quocanhcgd/Voron-0/VORON-0/STLs/V0_TopHat/TopHat_Panel_Mounting/For_3mm_Panels/3mm_TH_Lower_Corner_Clip_Right_x2.stl

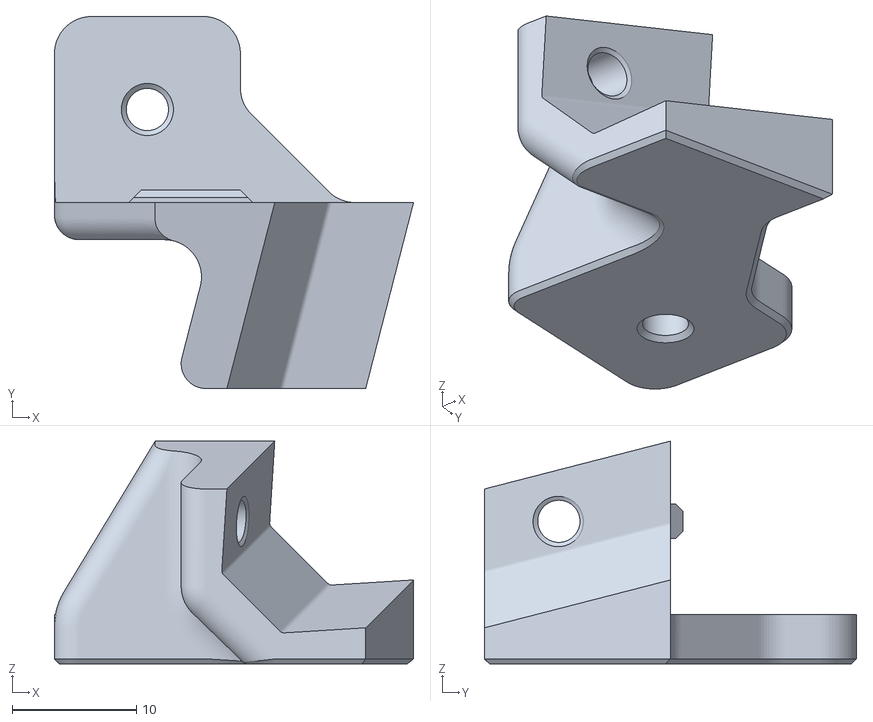
[picture p15: CAD file, 2021-10-14]
VORON-0/STLs/V0_TopHat/TopHat_Panel_Mounting/For_3mm_Panels/3mm_TH_Lower_Corner_Clip_Right_x2.stl
29.0 x 30.0 x 18.0
