quocanhcgd/Voron-0/VORON-0/STLs/V0_TopHat/Unibody_Tophat/Unibody_Tophat_x1.STL

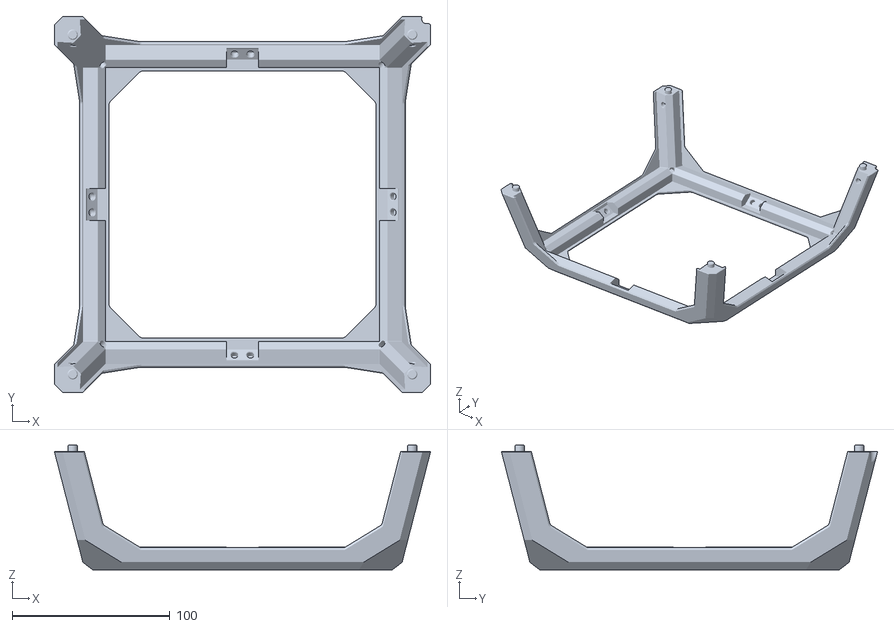
[picture p16: CAD file, 2021-10-14]
VORON-0/STLs/V0_TopHat/Unibody_Tophat/Unibody_Tophat_x1.STL
238.1 x 238.1 x 79.0
