quocanhcgd/Voron-0/VORON_Pocketwatch/STLs/[a]_Mount_Bracket_x1.STL

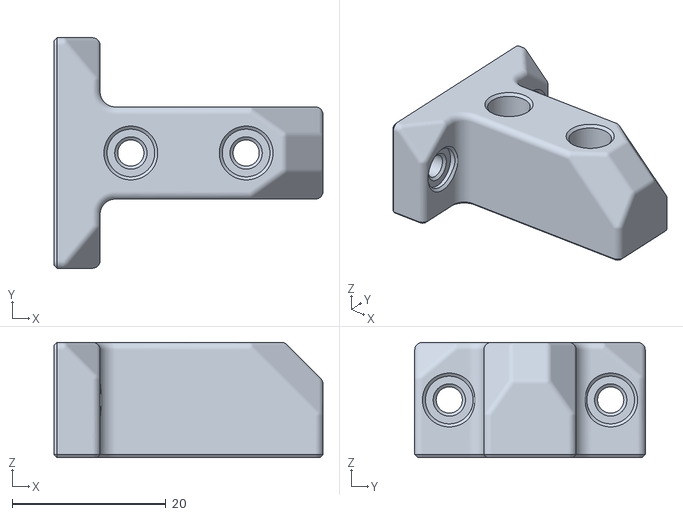
[picture p17: CAD file, 2021-10-14]
VORON_Pocketwatch/STLs/[a]_Mount_Bracket_x1.STL
35.0 x 30.0 x 15.0
