quocanhcgd/Voron-0/VORON-0/DXFs/Back_Panel_V0.DXF

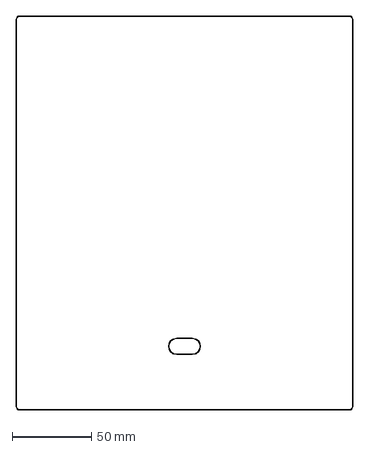
[picture p18: CAD file, 2021-10-14]
VORON-0/DXFs/Back_Panel_V0.DXF
212.0 x 248.0 mm
