quocanhcgd/Voron-0/VORON-0/STLs/[a]_A_Drive_Tensioner_x1.STL

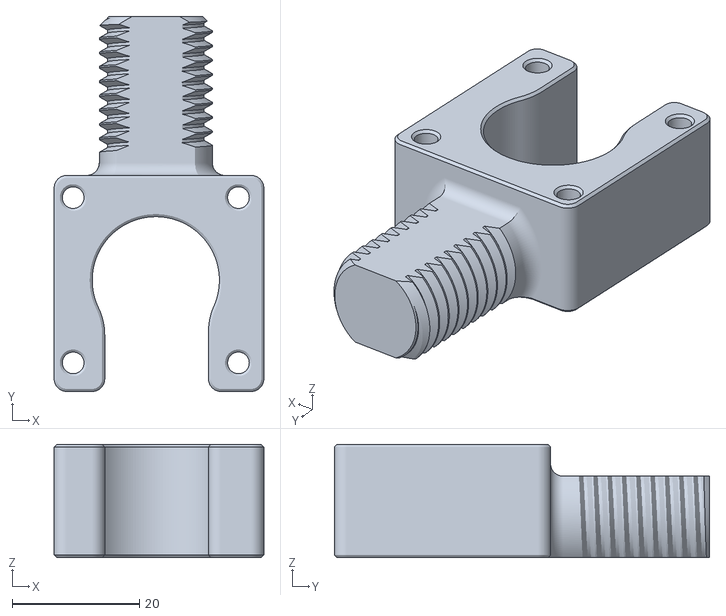
[picture p19: CAD file, 2021-10-14]
VORON-0/STLs/[a]_A_Drive_Tensioner_x1.STL
33.0 x 59.0 x 17.8
