quocanhcgd/Voron-0/VORON-0/STLs/Threaded_V6_Toolhead/Toolhead_Right_Threaded_V6_x1.STL

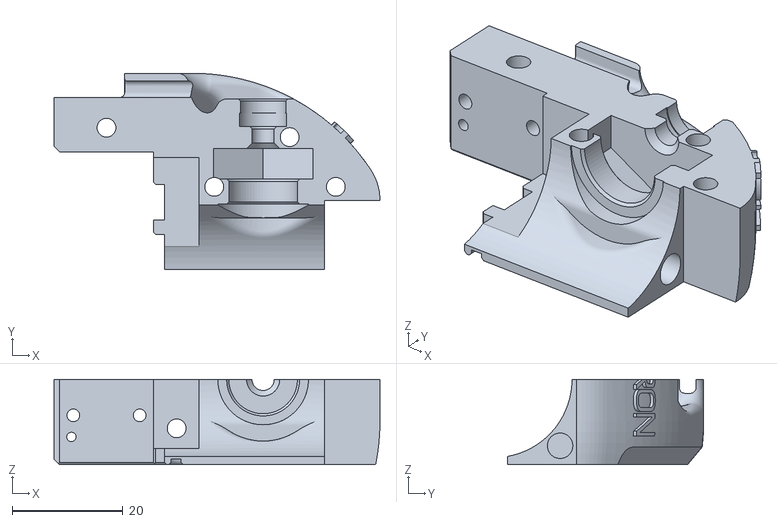
[picture p21: CAD file, 2021-10-14]
VORON-0/STLs/Threaded_V6_Toolhead/Toolhead_Right_Threaded_V6_x1.STL
59.0 x 35.6 x 15.4
