quocanhcgd/Voron-0/VORON-0/STLs/V0_Panel_Mounting/Door_Handle_x1.STL

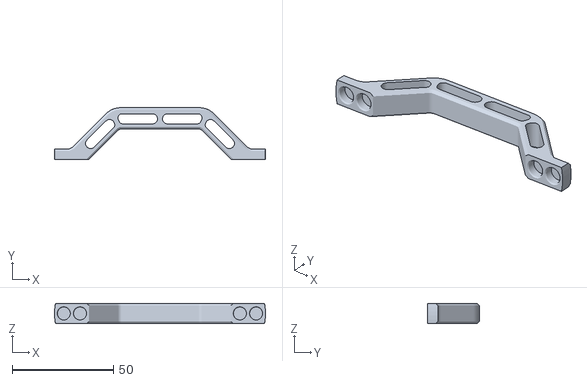
[picture p22: CAD file, 2021-10-14]
VORON-0/STLs/V0_Panel_Mounting/Door_Handle_x1.STL
104.2 x 25.5 x 10.0
