quocanhcgd/Voron-0/VORON-0/STLs/V0_Panel_Mounting/For_2.5mm_Panels/2point5mm_Top_Corner_Side_x2.STL

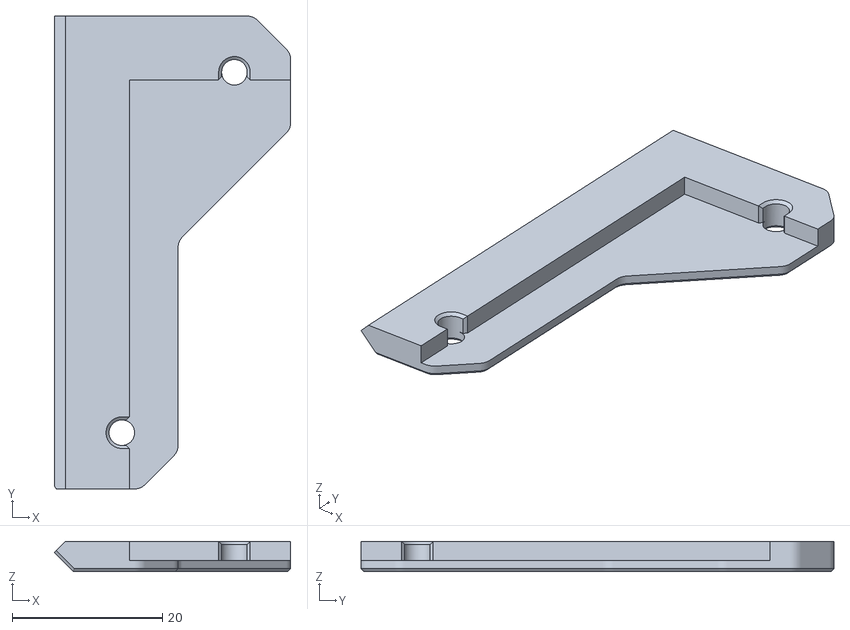
[picture p23: CAD file, 2021-10-14]
VORON-0/STLs/V0_Panel_Mounting/For_2.5mm_Panels/2point5mm_Top_Corner_Side_x2.STL
31.5 x 63.0 x 4.00
