quocanhcgd/Voron-0/VORON-0/STLs/V0_Panel_Mounting/For_2mm_Panels/2mm_Top_Corner_Rear_mirror_x1.STL

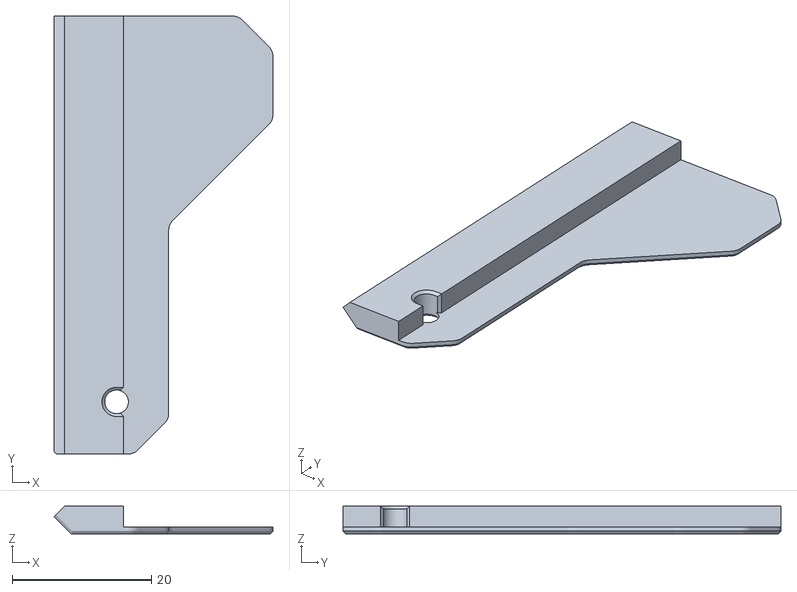
[picture p24: CAD file, 2021-10-14]
VORON-0/STLs/V0_Panel_Mounting/For_2mm_Panels/2mm_Top_Corner_Rear_mirror_x1.STL
31.5 x 63.0 x 4.00
