quocanhcgd/Voron-0/VORON-0/STLs/V0_Panel_Mounting/For_3mm_Panels/3mm_Top_Corner_Rear_x1.stl

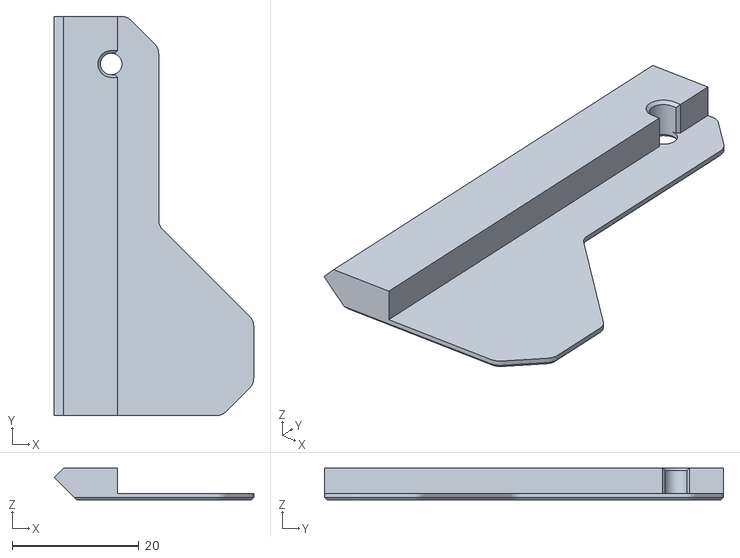
[picture p25: CAD file, 2021-10-14]
VORON-0/STLs/V0_Panel_Mounting/For_3mm_Panels/3mm_Top_Corner_Rear_x1.stl
31.5 x 63.0 x 5.00
