quocanhcgd/Voron-0/VORON-0/STLs/V0_TopHat/TopHat_Panel_Mounting/For_2.5mm_Panels/2point5mm_TH_Lower_Corner_Clip_Left_x2.STL

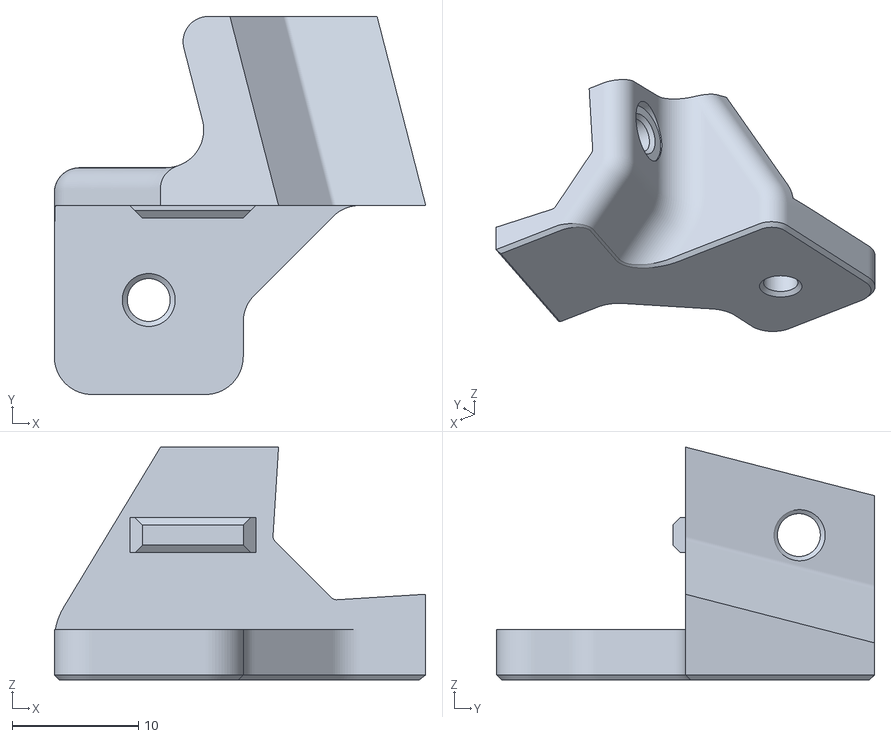
[picture p26: CAD file, 2021-10-14]
VORON-0/STLs/V0_TopHat/TopHat_Panel_Mounting/For_2.5mm_Panels/2point5mm_TH_Lower_Corner_Clip_Left_x2.STL
29.5 x 30.0 x 18.5
