quocanhcgd/Voron-0/VORON-0/STLs/V0_TopHat/TopHat_Panel_Mounting/For_2mm_Panels/2mm_TH_Mid_Clip_x4.STL

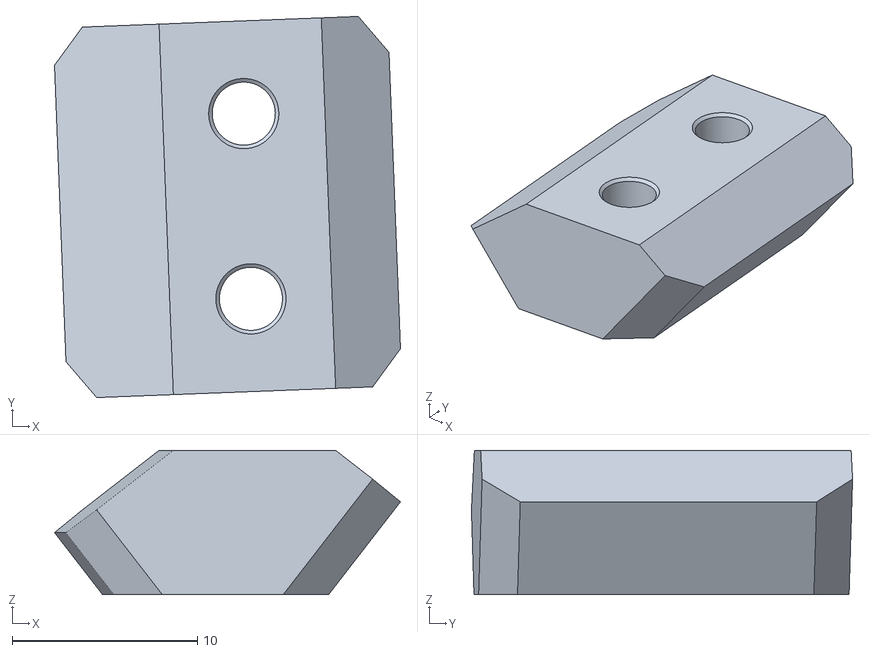
[picture p27: CAD file, 2021-10-14]
VORON-0/STLs/V0_TopHat/TopHat_Panel_Mounting/For_2mm_Panels/2mm_TH_Mid_Clip_x4.STL
18.7 x 20.6 x 7.78
