quocanhcgd/Voron-0/VORON-0/STLs/V0_TopHat/TopHat_Panel_Mounting/For_3mm_Panels/3mm_TH_Top_Corner_Clips_x4.STL

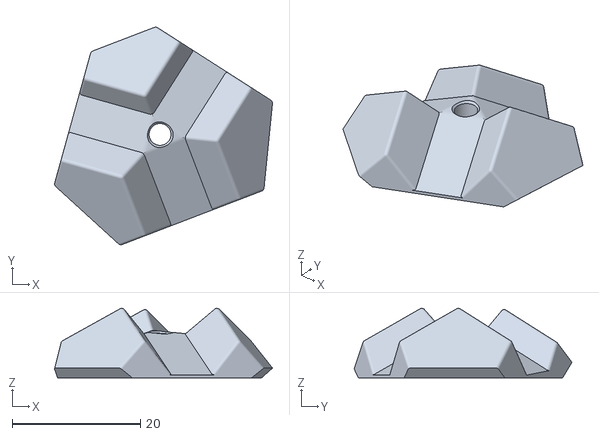
[picture p28: CAD file, 2021-10-14]
VORON-0/STLs/V0_TopHat/TopHat_Panel_Mounting/For_3mm_Panels/3mm_TH_Top_Corner_Clips_x4.STL
34.0 x 33.9 x 10.8
