quocanhcgd/Voron-0/VORON_Pocketwatch/STLs/[a]_Guidler_Door_x1.STL

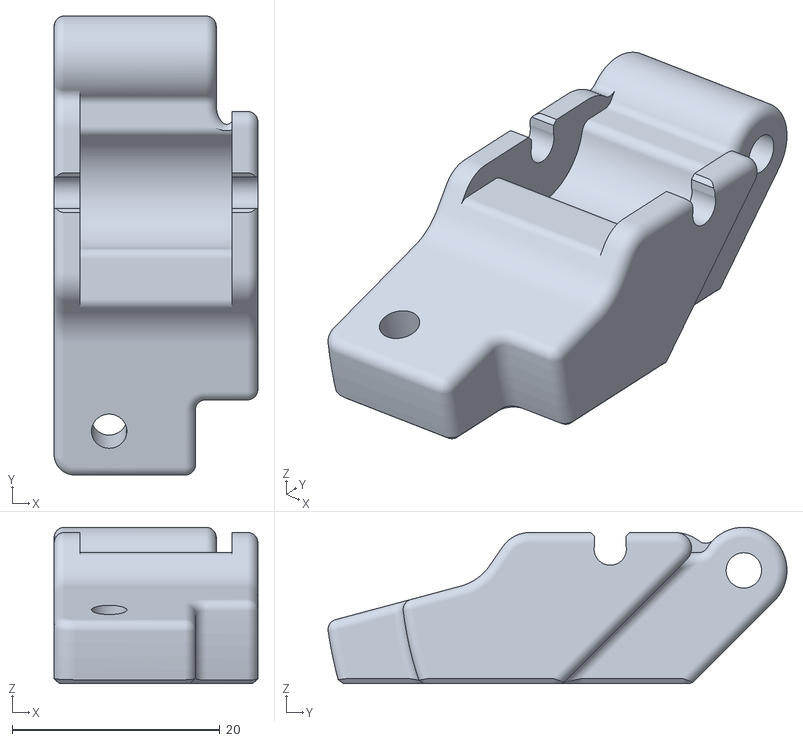
[picture p29: CAD file, 2021-10-14]
VORON_Pocketwatch/STLs/[a]_Guidler_Door_x1.STL
19.6 x 44.1 x 15.0
