quocanhcgd/Voron-0/VORON-0/DXFs/Mid_Panel_V0.DXF

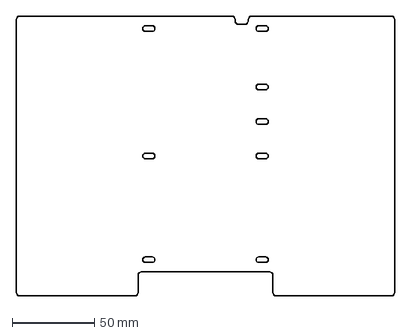
[picture p30: CAD file, 2021-10-14]
VORON-0/DXFs/Mid_Panel_V0.DXF
230.0 x 170.0 mm
