quocanhcgd/Voron-0/VORON-0/STLs/A_Drive_Frame_Top_x1.STL

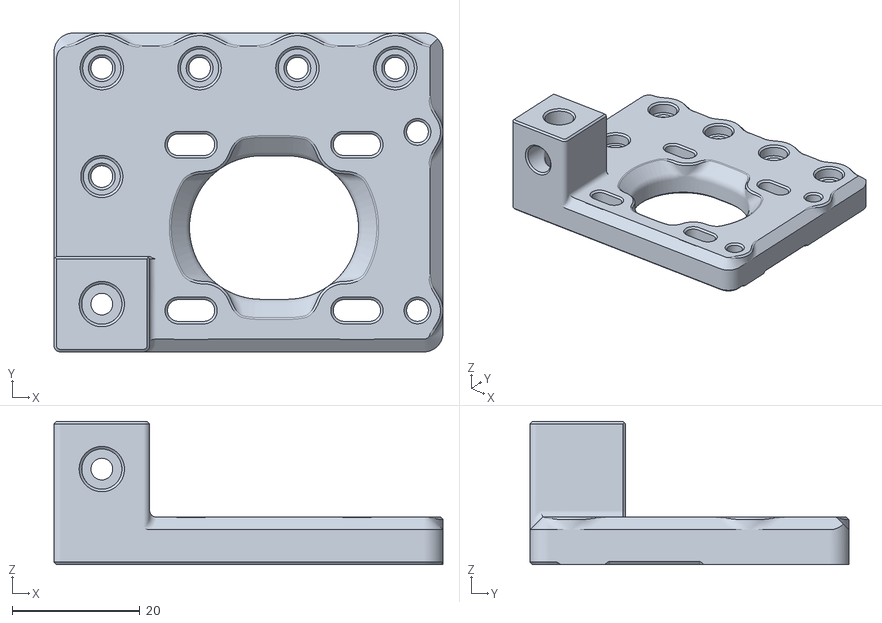
[picture p31: CAD file, 2021-10-14]
VORON-0/STLs/A_Drive_Frame_Top_x1.STL
61.0 x 50.0 x 22.5
