quocanhcgd/Voron-0/VORON-0/STLs/Threaded_V6_Toolhead/[a]_Toolhead_Blower_Duct_Left_TV6_x1.STL

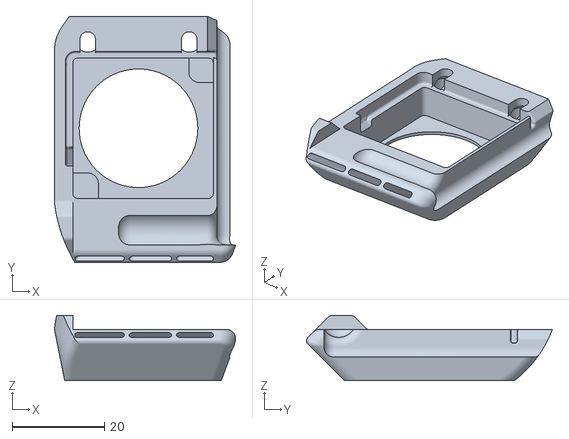
[picture p32: CAD file, 2021-10-14]
VORON-0/STLs/Threaded_V6_Toolhead/[a]_Toolhead_Blower_Duct_Left_TV6_x1.STL
39.3 x 53.3 x 14.1
