quocanhcgd/Voron-0/VORON-0/STLs/V0_Panel_Mounting/For_2.5mm_Panels/2point5mm_Bottom_Corner_Front_x1.STL

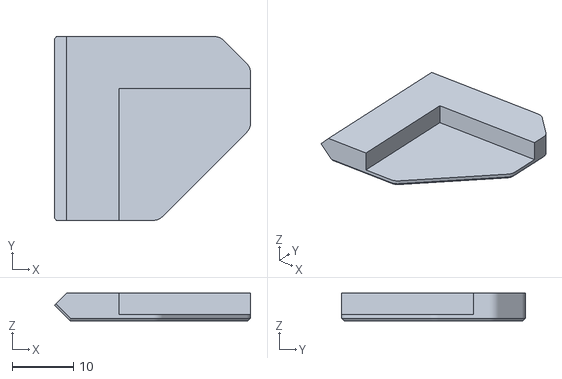
[picture p33: CAD file, 2021-10-14]
VORON-0/STLs/V0_Panel_Mounting/For_2.5mm_Panels/2point5mm_Bottom_Corner_Front_x1.STL
32.0 x 30.0 x 4.50
