quocanhcgd/Voron-0/VORON-0/STLs/V0_Panel_Mounting/For_3mm_Panels/3mm_Hinge_Top_A_x1.stl

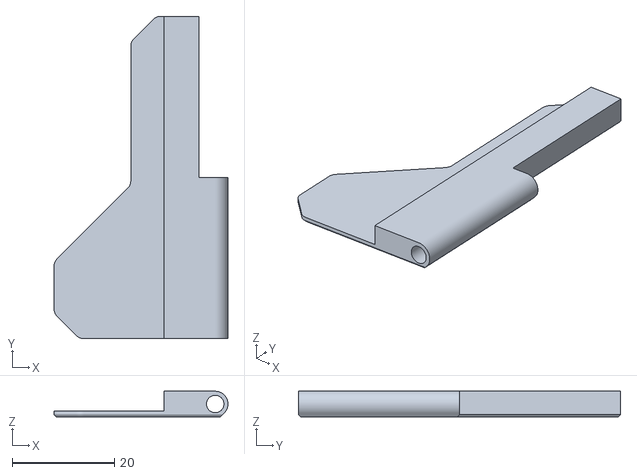
[picture p35: CAD file, 2021-10-14]
VORON-0/STLs/V0_Panel_Mounting/For_3mm_Panels/3mm_Hinge_Top_A_x1.stl
34.0 x 63.0 x 5.00
