quocanhcgd/Voron-0/VORON-0/STLs/V0_TopHat/TopHat_Panel_Mounting/For_2mm_Panels/2mm_TH_Top_Corner_Clips_x4.STL

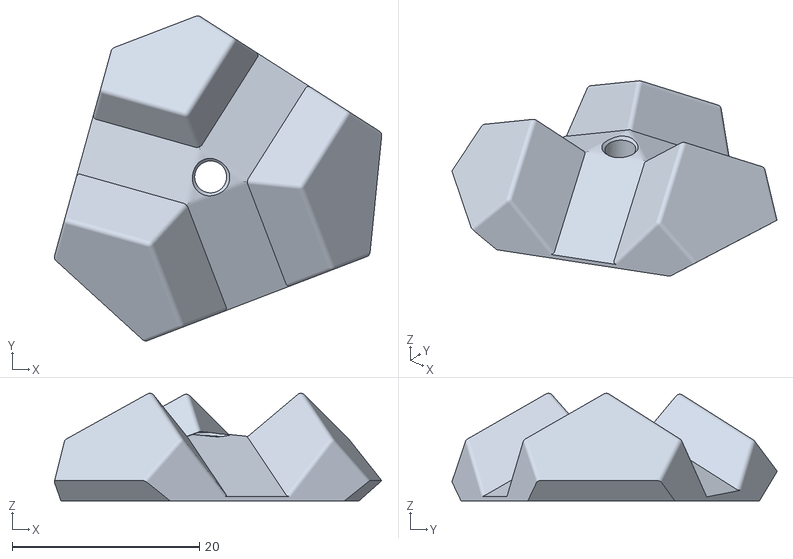
[picture p36: CAD file, 2021-10-14]
VORON-0/STLs/V0_TopHat/TopHat_Panel_Mounting/For_2mm_Panels/2mm_TH_Top_Corner_Clips_x4.STL
34.9 x 34.7 x 11.5
