quocanhcgd/Voron-0/VORON_Pocketwatch/STLs/[a]_Latch_Shuttle_x1.STL

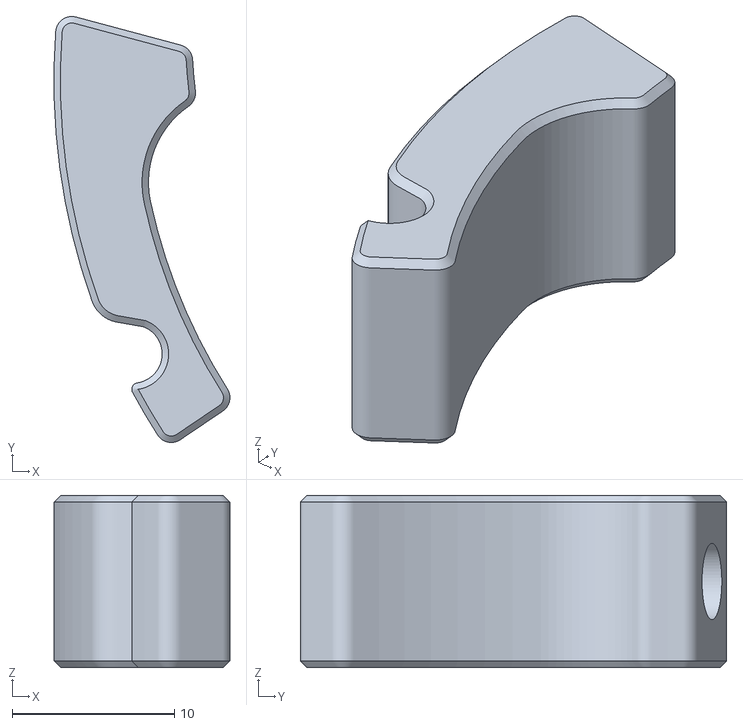
[picture p37: CAD file, 2021-10-14]
VORON_Pocketwatch/STLs/[a]_Latch_Shuttle_x1.STL
10.8 x 26.2 x 10.6
