quocanhcgd/Voron-0/VORON-0/DXFs/Deck_Panel_V0.DXF

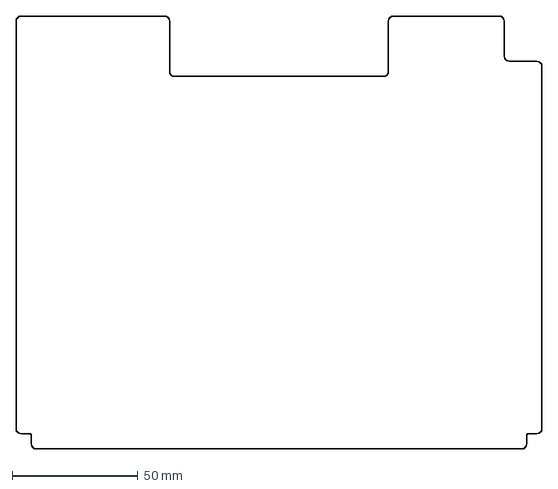
[picture p38: CAD file, 2021-10-14]
VORON-0/DXFs/Deck_Panel_V0.DXF
209.0 x 172.0 mm
