quocanhcgd/Voron-0/VORON-0/STLs/Front_Bed_Mount_x1.STL

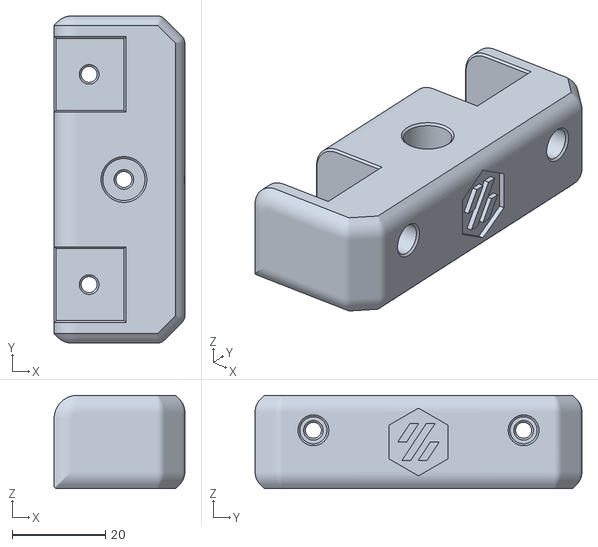
[picture p39: CAD file, 2021-10-14]
VORON-0/STLs/Front_Bed_Mount_x1.STL
28.0 x 70.0 x 20.0
