quocanhcgd/Voron-0/VORON-0/STLs/V0_TopHat/TopHat_Panel_Mounting/For_3mm_Panels/3mm_TH_Mid_Clip_x4.STL

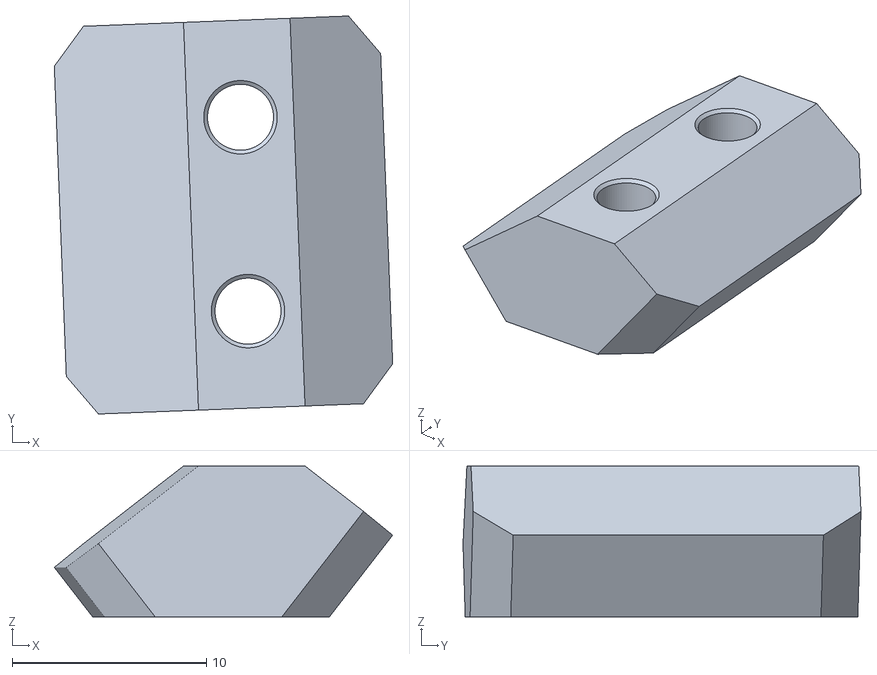
[picture p41: CAD file, 2021-10-14]
VORON-0/STLs/V0_TopHat/TopHat_Panel_Mounting/For_3mm_Panels/3mm_TH_Mid_Clip_x4.STL
17.4 x 20.5 x 7.78
