quocanhcgd/Voron-0/VORON_Pocketwatch/STLs/Pocketwatch_Guts_x1.STL

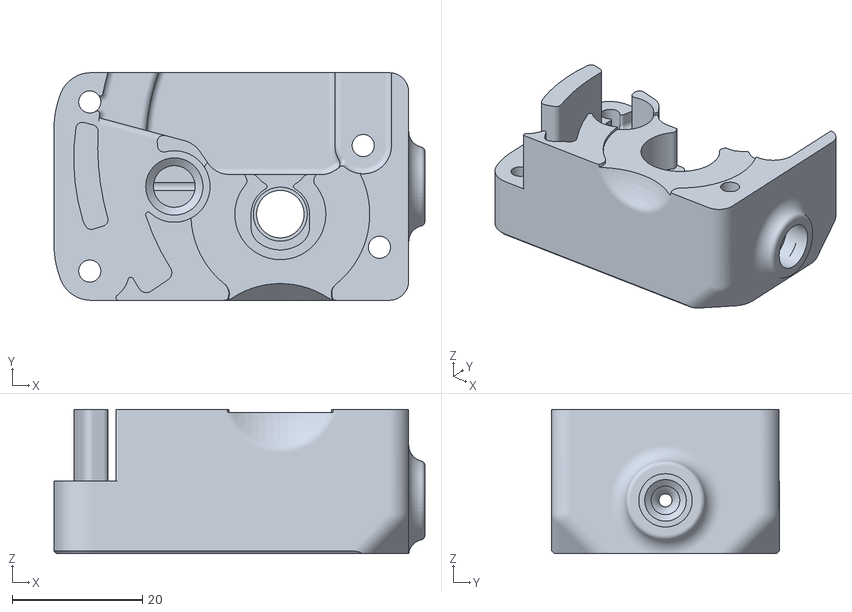
[picture p42: CAD file, 2021-10-14]
VORON_Pocketwatch/STLs/Pocketwatch_Guts_x1.STL
57.0 x 35.0 x 22.2
