quocanhcgd/Voron-0/VORON-0/DXFs/TopHat_Side_Panel.DXF

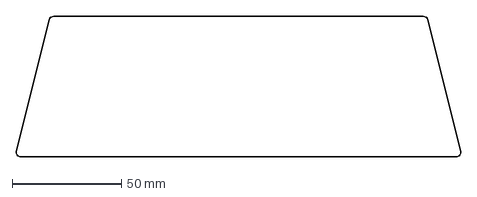
[picture p43: CAD file, 2021-10-14]
VORON-0/DXFs/TopHat_Side_Panel.DXF
204.0 x 64.4 mm
