quocanhcgd/Voron-0/VORON-0/STLs/XY_Joint_Right_Top_x1.STL

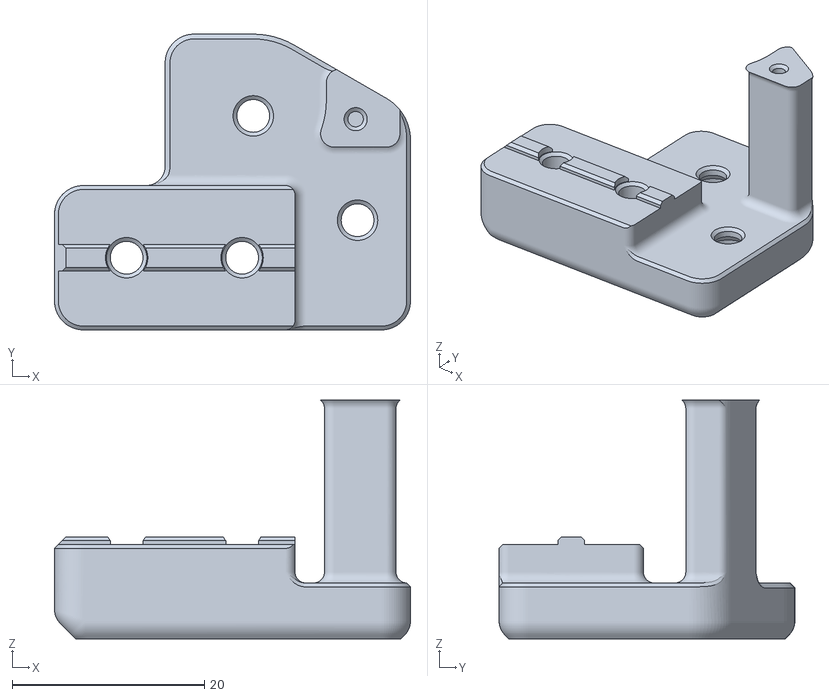
[picture p45: CAD file, 2021-10-14]
VORON-0/STLs/XY_Joint_Right_Top_x1.STL
37.0 x 30.7 x 24.8
