quocanhcgd/Voron-0/VORON_Pocketwatch/STLs/pw_motor_spacer_(only_needed_if_not_using_motor_from_bom).STL

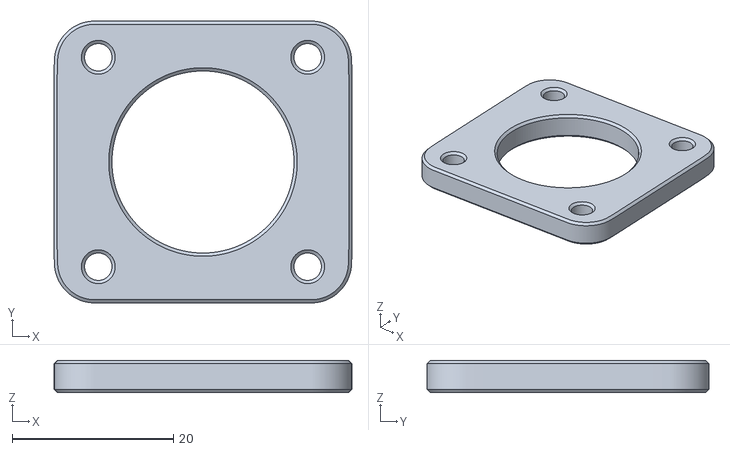
[picture p46: CAD file, 2021-10-14]
VORON_Pocketwatch/STLs/pw_motor_spacer_(only_needed_if_not_using_motor_from_bom).STL
37.0 x 35.0 x 4.00
