quocanhcgd/Voron-0/VORON-0/STLs/B_Idler_Top_x1.STL

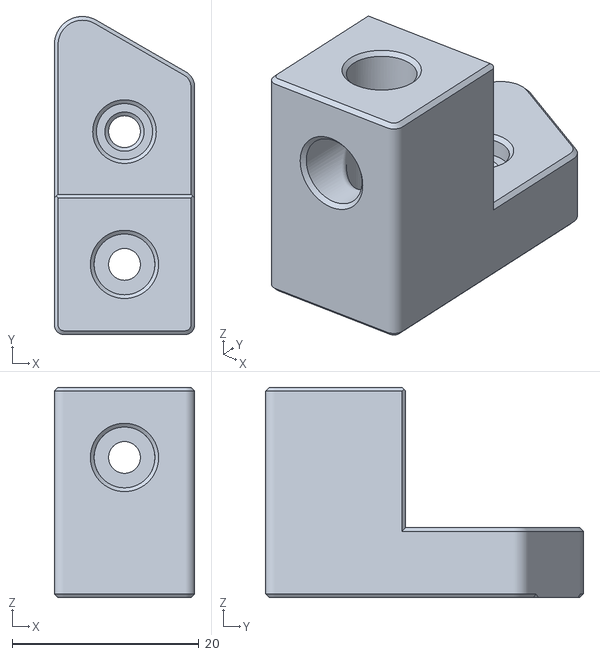
[picture p47: CAD file, 2021-10-14]
VORON-0/STLs/B_Idler_Top_x1.STL
15.0 x 34.0 x 22.5
