quocanhcgd/Voron-0/VORON_Pocketwatch/STLs/[a]_Latch_x1.STL

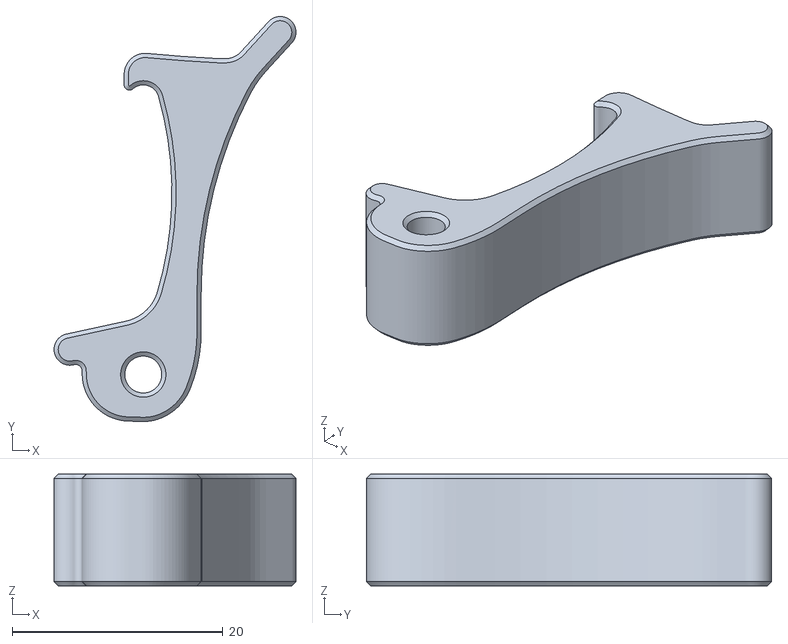
[picture p48: CAD file, 2021-10-14]
VORON_Pocketwatch/STLs/[a]_Latch_x1.STL
23.0 x 38.5 x 10.6
