quocanhcgd/Voron-0/VORON-0/STLs/[a]_Foot_Rear_x2.STL

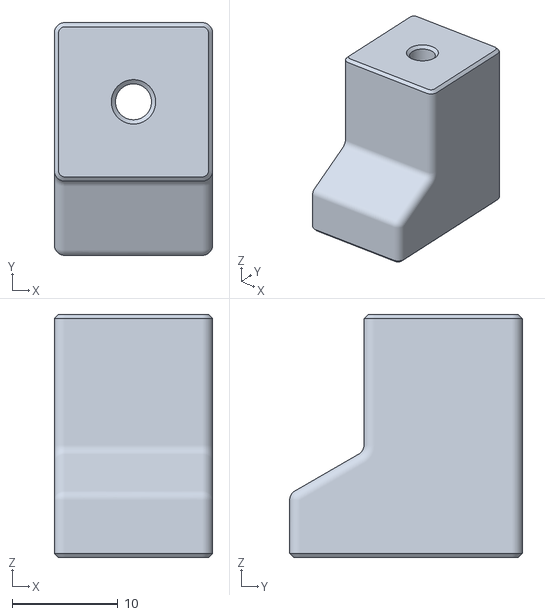
[picture p49: CAD file, 2021-10-14]
VORON-0/STLs/[a]_Foot_Rear_x2.STL
15.0 x 22.0 x 23.0
