quocanhcgd/Voron-0/VORON-0/STLs/V0_Panel_Mounting/For_2mm_Panels/2mm_Hinge_Top_B_x1.STL

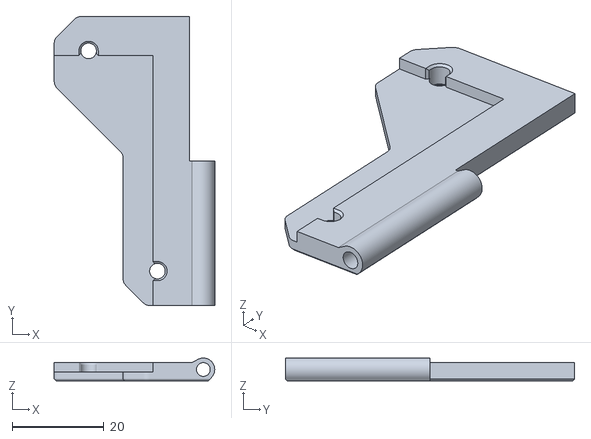
[picture p50: CAD file, 2021-10-14]
VORON-0/STLs/V0_Panel_Mounting/For_2mm_Panels/2mm_Hinge_Top_B_x1.STL
35.0 x 63.0 x 5.00
