quocanhcgd/Voron-0/VORON-0/STLs/V0_Panel_Mounting/For_3mm_Panels/3mm_Hinge_Bottom_B_x1.stl

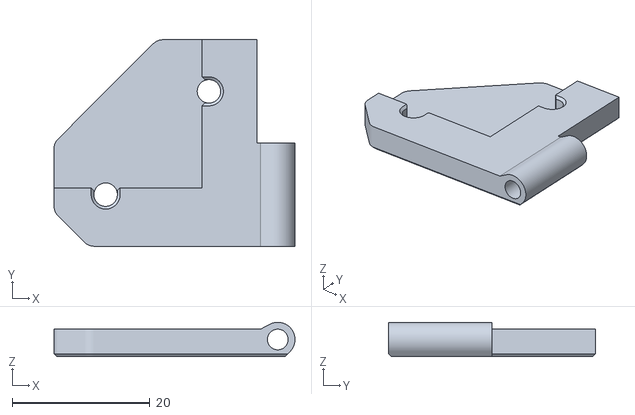
[picture p51: CAD file, 2021-10-14]
VORON-0/STLs/V0_Panel_Mounting/For_3mm_Panels/3mm_Hinge_Bottom_B_x1.stl
35.0 x 30.0 x 5.00
