quocanhcgd/Voron-0/VORON_Pocketwatch/STLs/Motor_Frame_x1.STL

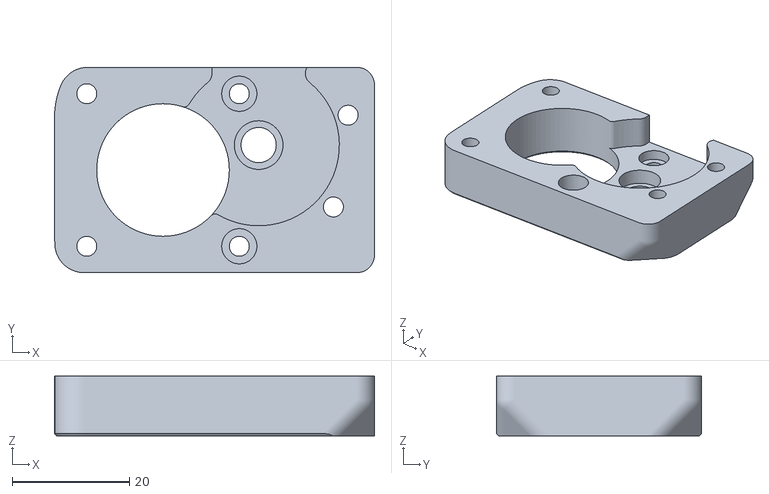
[picture p52: CAD file, 2021-10-14]
VORON_Pocketwatch/STLs/Motor_Frame_x1.STL
54.5 x 35.0 x 10.2
