quocanhcgd/Voron-0/VORON-0/STLs/[a]_Foot_Front_x2.stl

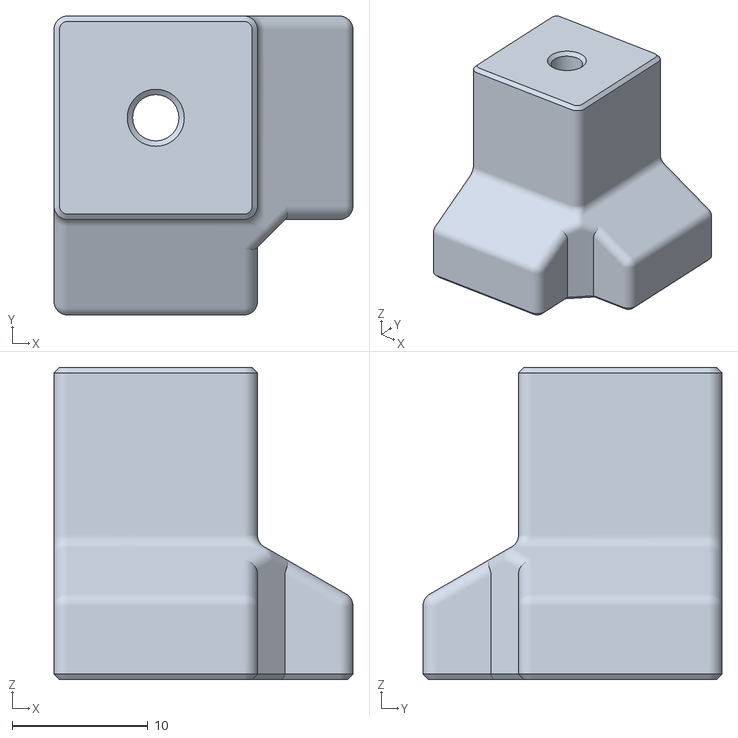
[picture p53: CAD file, 2021-10-14]
VORON-0/STLs/[a]_Foot_Front_x2.stl
22.0 x 22.0 x 23.0
