quocanhcgd/Voron-0/VORON-0/STLs/XY_Joint_Left_Bottom_x1.STL

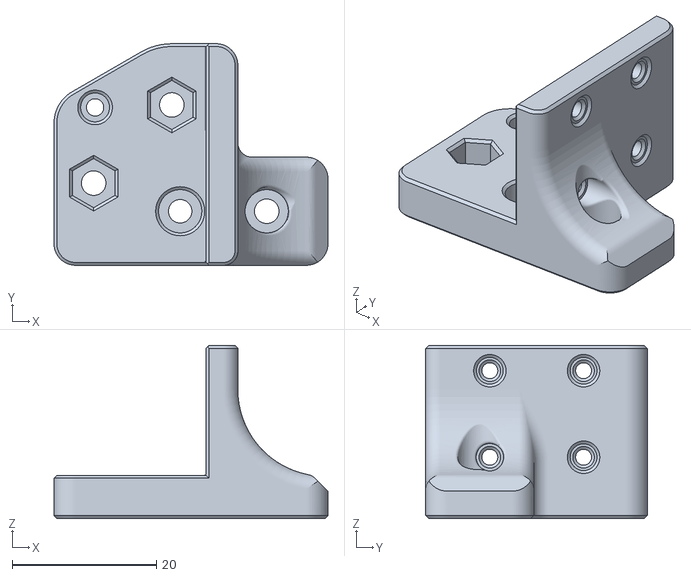
[picture p55: CAD file, 2021-10-14]
VORON-0/STLs/XY_Joint_Left_Bottom_x1.STL
38.0 x 30.7 x 24.0
