quocanhcgd/Voron-0/VORON-0/STLs/Spool_Holder_V0_x1.STL

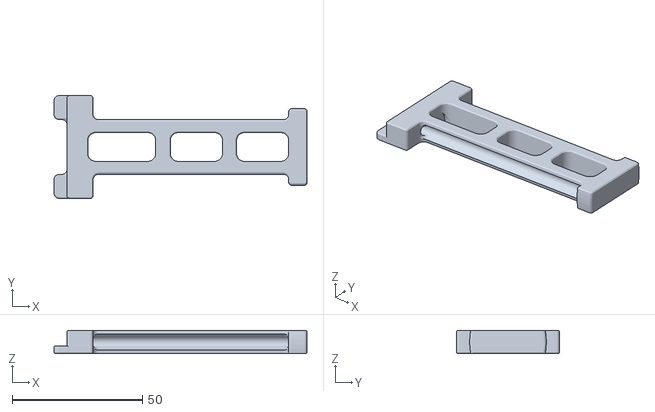
[picture p56: CAD file, 2021-10-14]
VORON-0/STLs/Spool_Holder_V0_x1.STL
97.0 x 39.4 x 9.00
