quocanhcgd/Voron-0/VORON-0/STLs/V0_Panel_Mounting/For_2.5mm_Panels/2point5mm_Middle_Clip_x9.STL

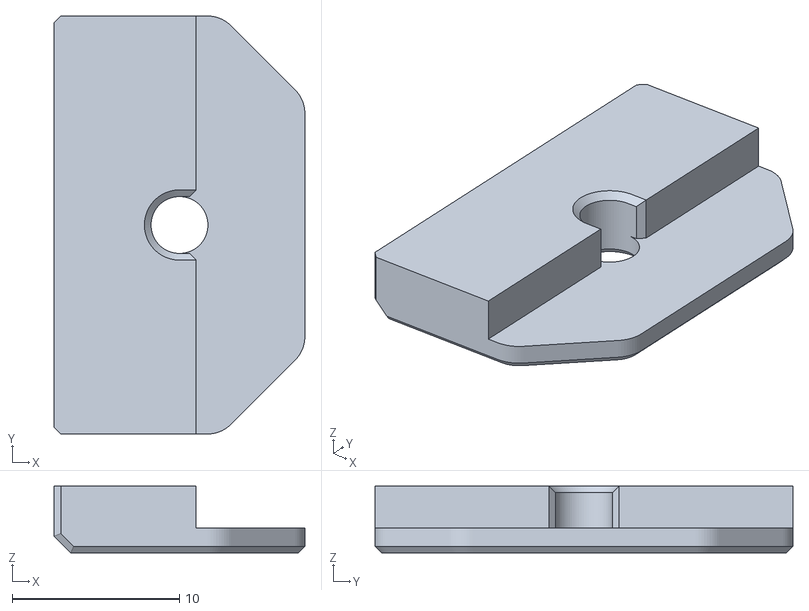
[picture p57: CAD file, 2021-10-14]
VORON-0/STLs/V0_Panel_Mounting/For_2.5mm_Panels/2point5mm_Middle_Clip_x9.STL
15.0 x 25.0 x 4.00
