quocanhcgd/Voron-0/VORON-0/STLs/V0_Panel_Mounting/For_2mm_Panels/2mm_Bottom_Corner_Rear_mirror_x1.STL

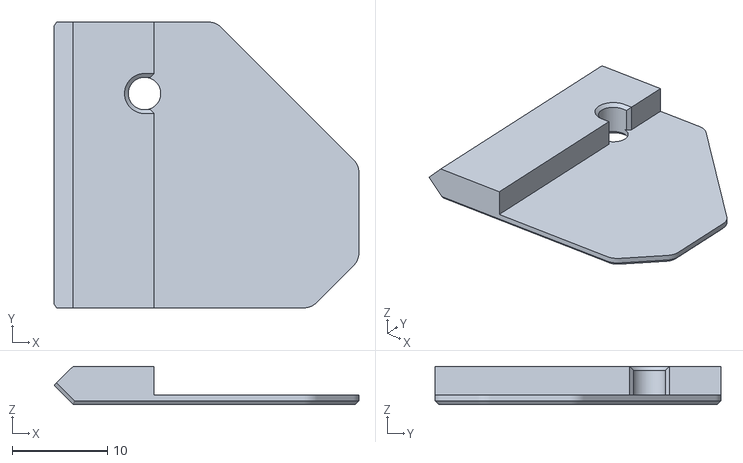
[picture p59: CAD file, 2021-10-14]
VORON-0/STLs/V0_Panel_Mounting/For_2mm_Panels/2mm_Bottom_Corner_Rear_mirror_x1.STL
32.0 x 30.0 x 4.00
