quocanhcgd/Voron-0/VORON-0/STLs/Skirt_x3.STL

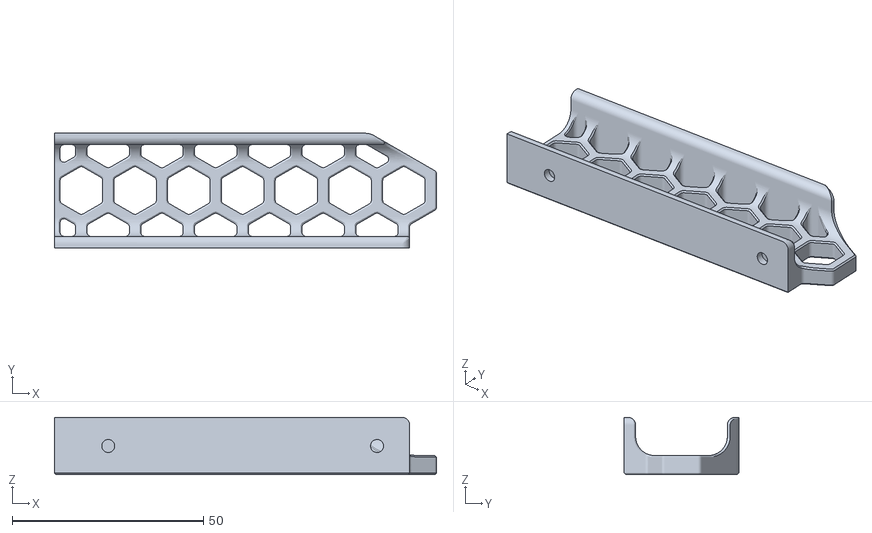
[picture p60: CAD file, 2021-10-14]
VORON-0/STLs/Skirt_x3.STL
100.0 x 30.0 x 15.0
