quocanhcgd/Voron-0/VORON-0/STLs/[a]_Endstop_Strike_Block_x1.STL

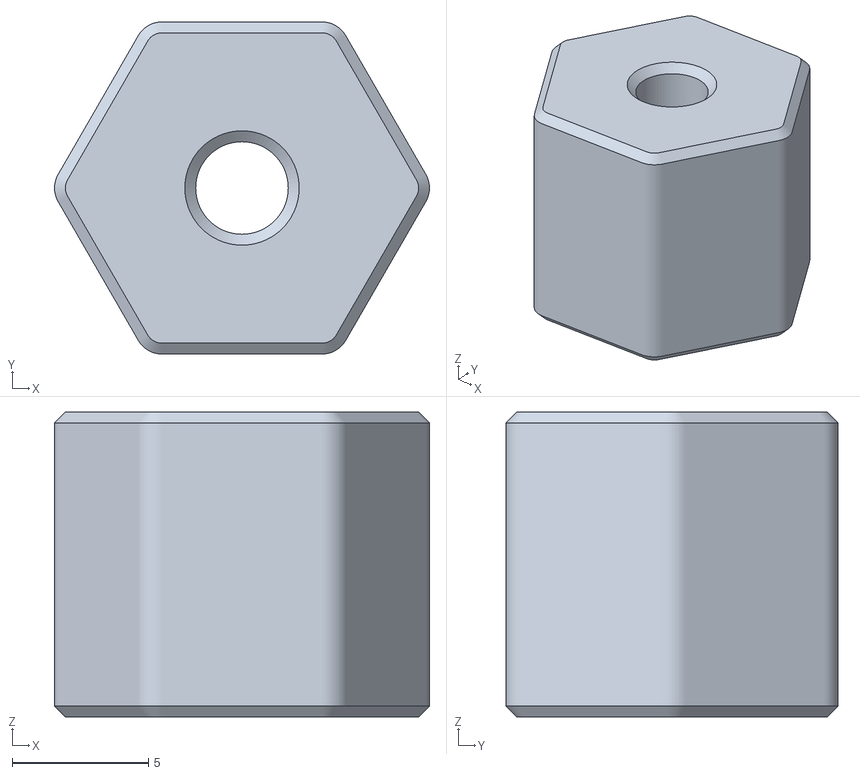
[picture p61: CAD file, 2021-10-14]
VORON-0/STLs/[a]_Endstop_Strike_Block_x1.STL
13.8 x 12.2 x 11.2
