quocanhcgd/Voron-0/VORON-0/STLs/V0_Panel_Mounting/For_3mm_Panels/3mm_Middle_Clip_x9.stl

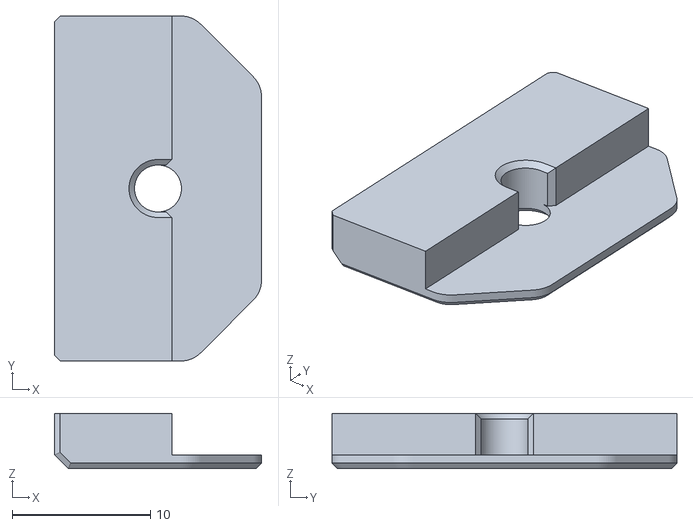
[picture p62: CAD file, 2021-10-14]
VORON-0/STLs/V0_Panel_Mounting/For_3mm_Panels/3mm_Middle_Clip_x9.stl
15.0 x 25.0 x 4.00
