quocanhcgd/Voron-0/VORON-0/STLs/RPi_Frame_x1.stl

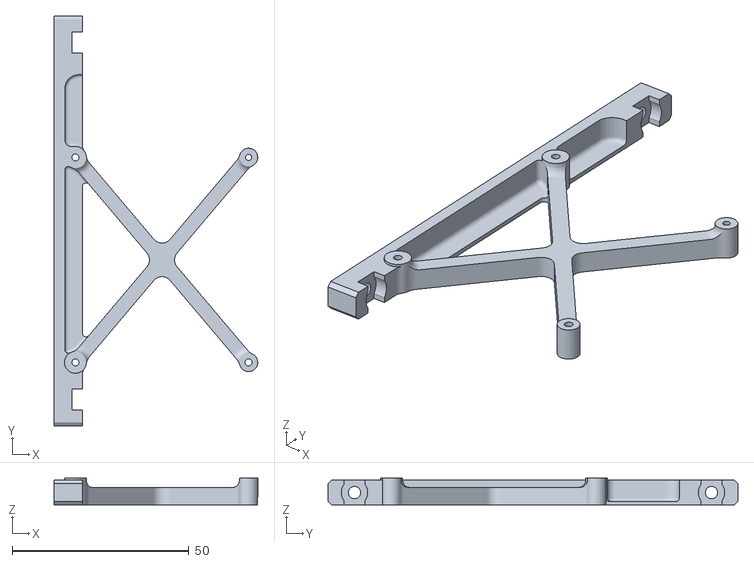
[picture p63: CAD file, 2021-10-14]
VORON-0/STLs/RPi_Frame_x1.stl
57.6 x 116.0 x 7.60
