quocanhcgd/Voron-0/VORON-0/STLs/MGN7_Rail_Guide_x2.STL

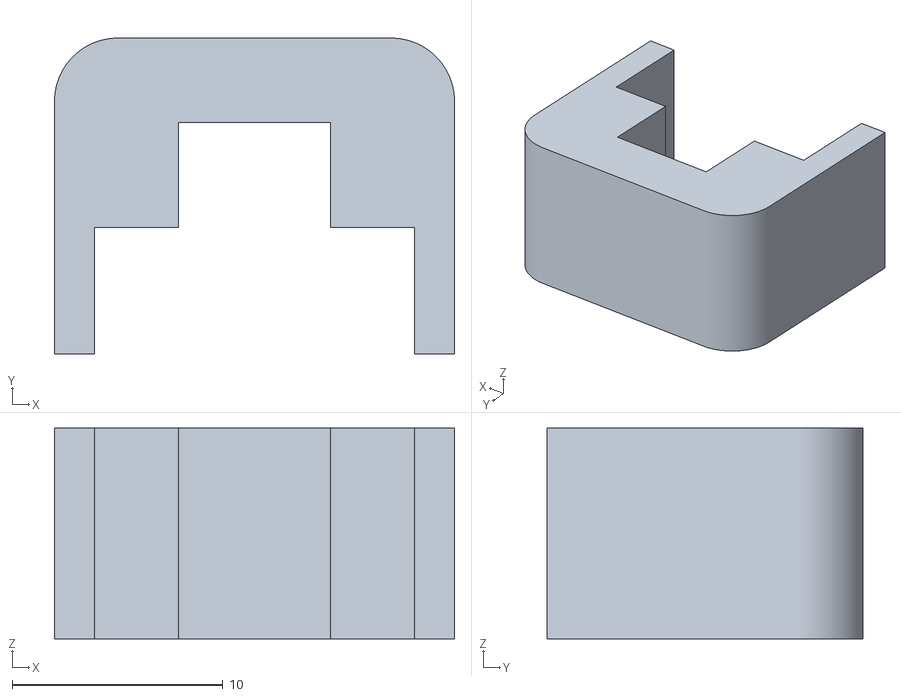
[picture p64: CAD file, 2021-10-14]
VORON-0/STLs/MGN7_Rail_Guide_x2.STL
19.0 x 15.0 x 10.0
