quocanhcgd/Voron-0/VORON-0/STLs/B_Drive_Frame_Bottom_x1.STL

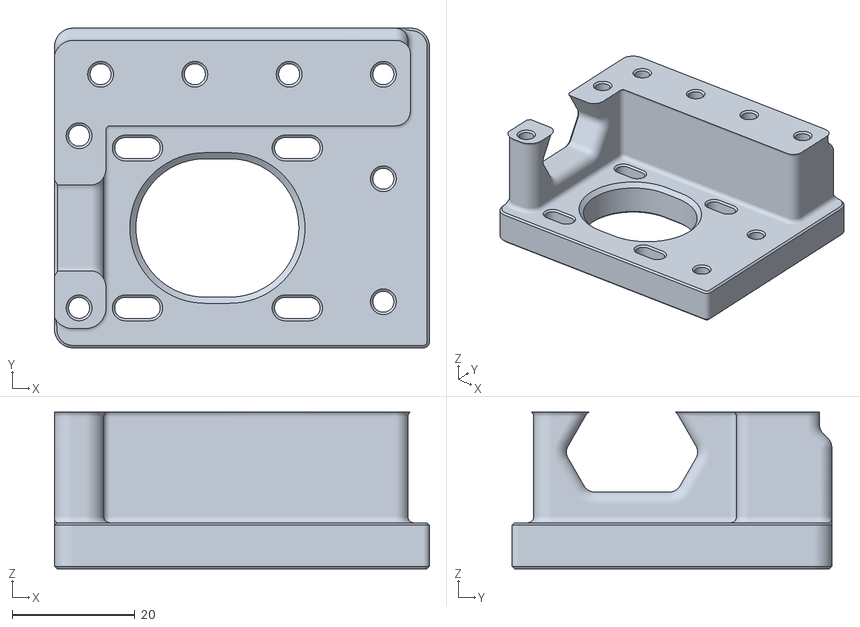
[picture p65: CAD file, 2021-10-14]
VORON-0/STLs/B_Drive_Frame_Bottom_x1.STL
61.0 x 52.0 x 25.5
