quocanhcgd/Voron-0/VORON-0/STLs/Z_Motor_Mount_x1.STL

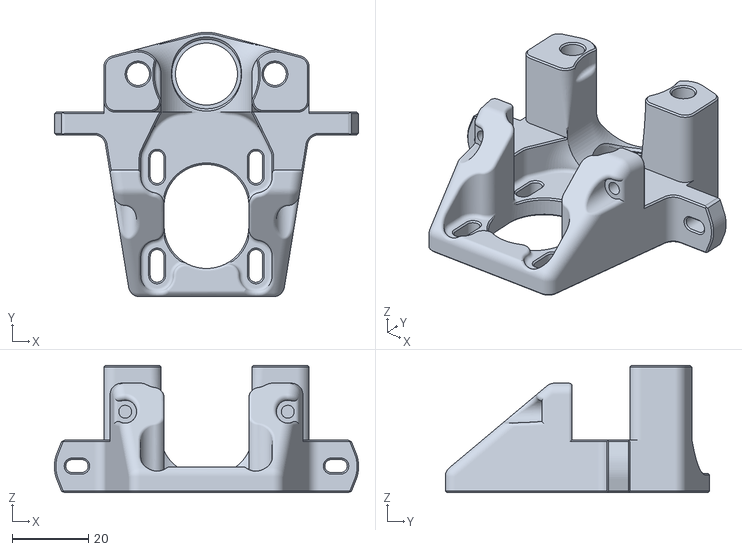
[picture p66: CAD file, 2021-10-14]
VORON-0/STLs/Z_Motor_Mount_x1.STL
80.0 x 69.6 x 33.5
