quocanhcgd/Voron-0/VORON-0/STLs/V0_Extrusion_Drilling_Guide_x1.STL

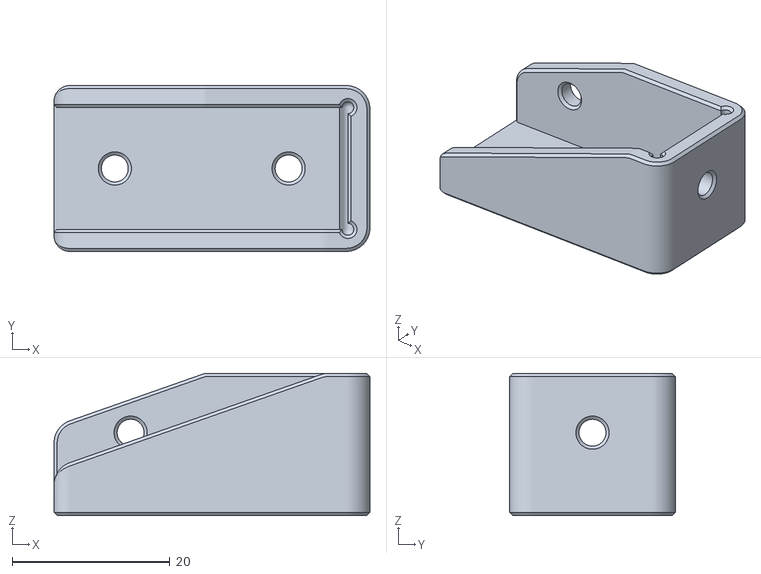
[picture p68: CAD file, 2021-10-14]
VORON-0/STLs/V0_Extrusion_Drilling_Guide_x1.STL
40.0 x 21.0 x 18.0
