quocanhcgd/Voron-0/VORON-0/STLs/[a]_9mm_Printed_Spacer_x6.STL

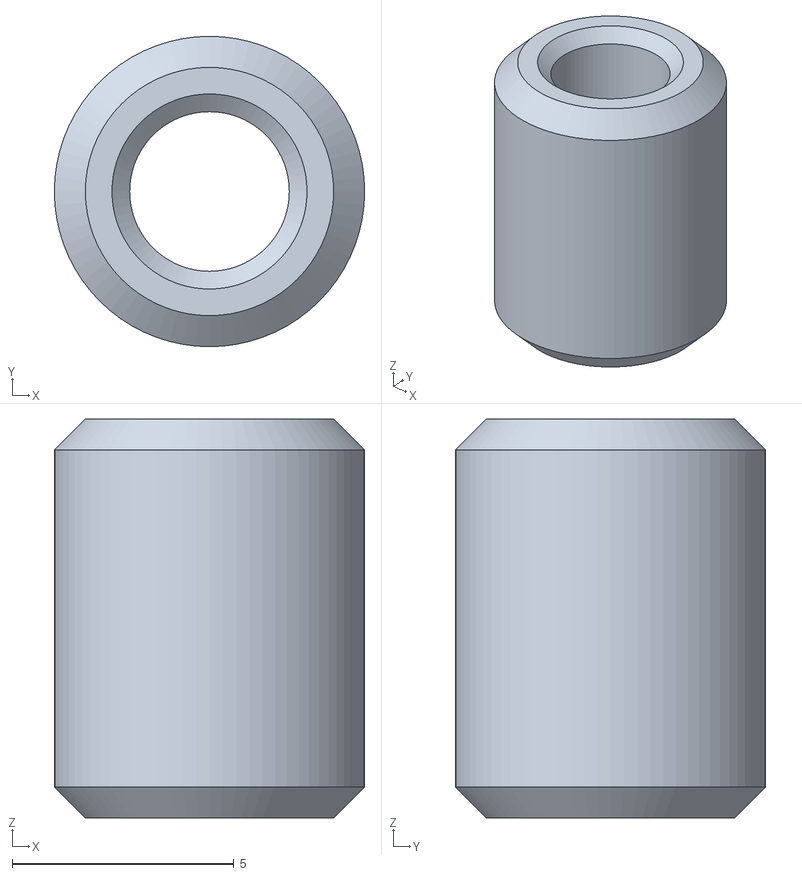
[picture p69: CAD file, 2021-10-14]
VORON-0/STLs/[a]_9mm_Printed_Spacer_x6.STL
7.00 x 7.00 x 9.00
