quocanhcgd/Voron-0/VORON-0/STLs/[a]_Belt_Retension_Block_x1.stl

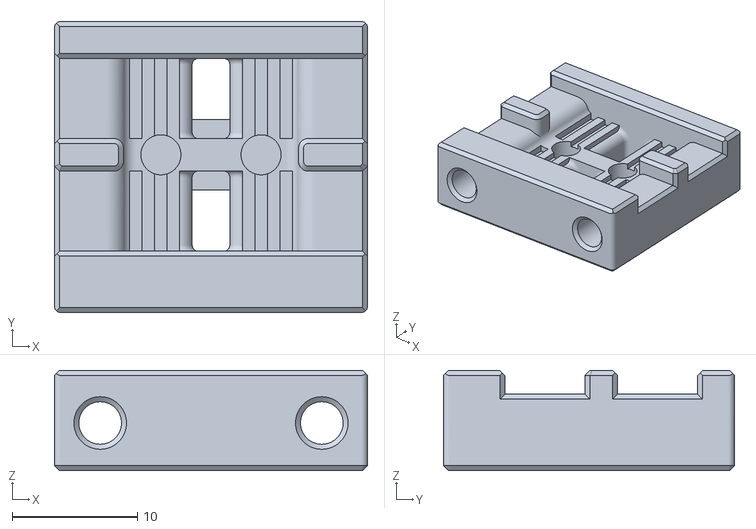
[picture p71: CAD file, 2021-10-14]
VORON-0/STLs/[a]_Belt_Retension_Block_x1.stl
25.0 x 23.2 x 8.00
