quocanhcgd/Voron-0/VORON-0/STLs/[a]_Z_Endstop_Mount_x1.STL

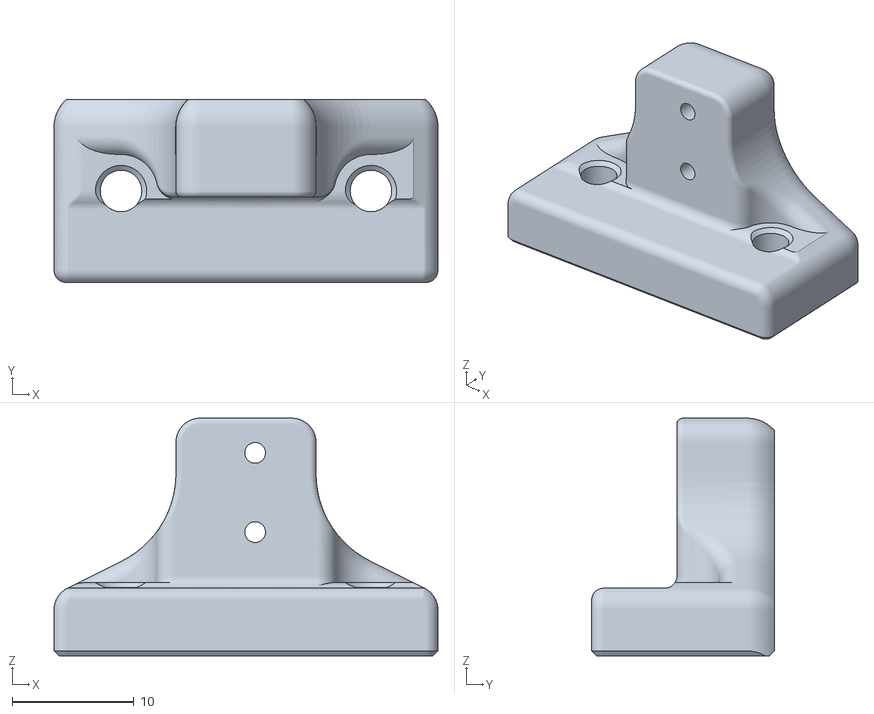
[picture p72: CAD file, 2021-10-14]
VORON-0/STLs/[a]_Z_Endstop_Mount_x1.STL
31.5 x 15.0 x 19.5
